juarendra/Ergotravel-MOD-XIAO/HARDWARE/SCH-PCB/models/PG1350-socket.STEP

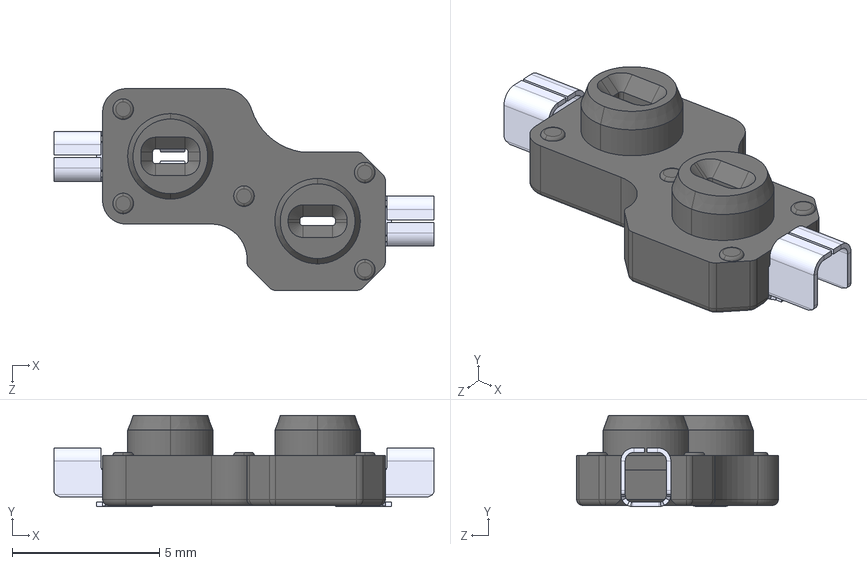
[picture p21: CAD file, 2024-07-08]
HARDWARE/SCH-PCB/models/PG1350-socket.STEP
12.9 x 3.09 x 6.85 mm
pin x 2
socket
