juarendra/Ergotravel-MOD-XIAO/HARDWARE/SCH-PCB/models/TM040040_Overlay.STEP

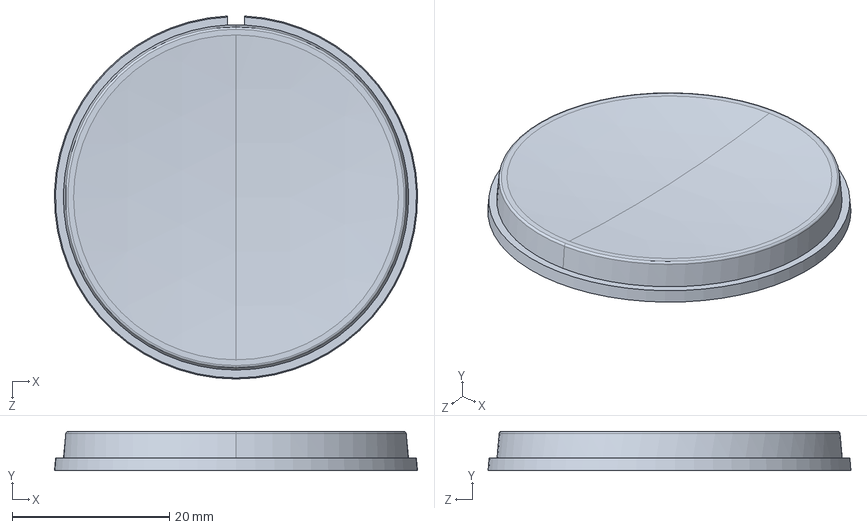
[picture p22: CAD file, 2024-07-08]
HARDWARE/SCH-PCB/models/TM040040_Overlay.STEP
46.1 x 5.00 x 46.1 mm
